masonbutler/UsbMidiAudioControl/Firmware/MidiMessages.h

#ifndef MIDIMESSAGES_H_
#define MIDIMESSAGES_H_

#define MIDI_NOTE_OFF			0x80
#define MIDI_NOTE_ON			0x90
#define MIDI_AFTERTOUCH			0xA0
#define MIDI_CC					0xB0
#define MIDI_PATCH_CHANGE		0xC0
#define MIDI_CHANNEL_PRESSURE	0xD0
#define MIDI_PITCH_BEND			0xE0
#define MIDI_MISC_CMD			0xF0



#endif
